SendToSouthEast/SIPI2/README/image-20230415004435432.png

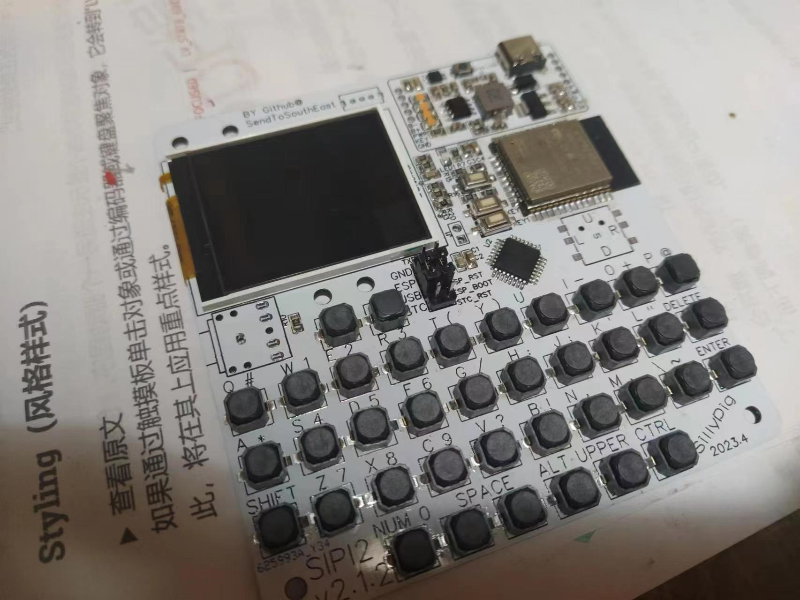
README/image-20230415004435432.png
