SendToSouthEast/SIPI2/README/image-20230421204047244.png

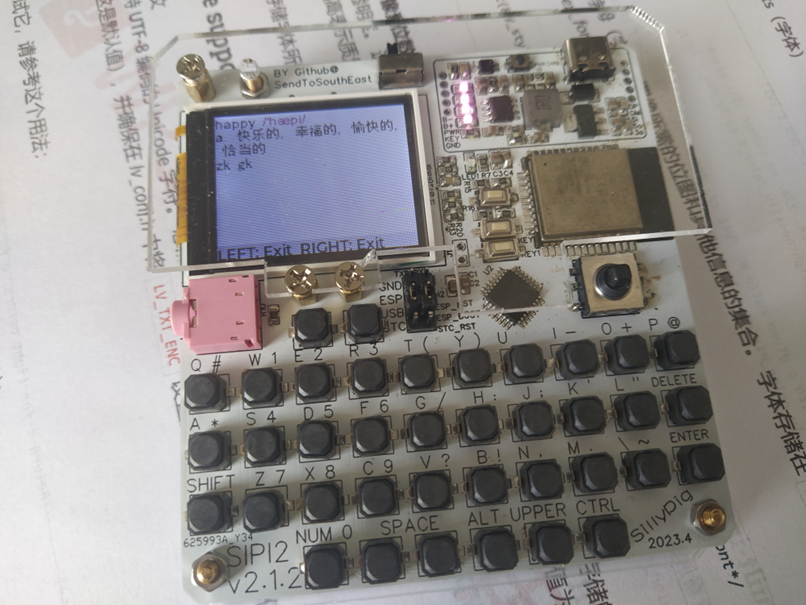
README/image-20230421204047244.png
