SendToSouthEast/SIPI2/SIPI2_ESP32/main/arial.c

/*******************************************************************************
 * Size: 12 px
 * Bpp: 1
 * Opts: 
 ******************************************************************************/

#ifdef LV_LVGL_H_INCLUDE_SIMPLE
#include "lvgl.h"
#else
#include "lvgl/lvgl.h"
#endif

#ifndef ARIAL
#define ARIAL 1
#endif

#if ARIAL

/*-----------------
 *    BITMAPS
 *----------------*/

/*Store the image of the glyphs*/
static LV_ATTRIBUTE_LARGE_CONST const uint8_t glyph_bitmap[] = {
    /* U+0020 " " */
    0x0,

    /* U+0027 "'" */
    0xe0,

    /* U+002C "," */
    0xc0,

    /* U+002D "-" */
    0xe0,

    /* U+002E "." */
    0x80,

    /* U+002F "/" */
    0x24, 0xa4, 0xa4,

    /* U+003A ":" */
    0x84,

    /* U+0041 "A" */
    0x18, 0x18, 0x2c, 0x24, 0x64, 0x7e, 0x42, 0x83,

    /* U+0042 "B" */
    0xfa, 0x18, 0x7e, 0x86, 0x18, 0x7e,

    /* U+0043 "C" */
    0x3c, 0x8e, 0x4, 0x8, 0x10, 0x51, 0x9e,

    /* U+0044 "D" */
    0xf9, 0xa, 0xc, 0x18, 0x30, 0x61, 0x7c,

    /* U+0045 "E" */
    0xfe, 0x8, 0x3f, 0x82, 0x8, 0x3f,

    /* U+0046 "F" */
    0xfe, 0x8, 0x3e, 0x82, 0x8, 0x20,

    /* U+0047 "G" */
    0x3c, 0x43, 0x81, 0x80, 0x8f, 0x81, 0x41, 0x3e,

    /* U+0048 "H" */
    0x83, 0x6, 0xf, 0xf8, 0x30, 0x60, 0xc1,

    /* U+0049 "I" */
    0xff,

    /* U+004A "J" */
    0x8, 0x42, 0x10, 0x86, 0x2e,

    /* U+004B "K" */
    0x85, 0x12, 0x47, 0xd, 0x11, 0x23, 0x43,

    /* U+004C "L" */
    0x84, 0x21, 0x8, 0x42, 0x1f,

    /* U+004D "M" */
    0xc3, 0xc3, 0xc3, 0xa5, 0xa5, 0x99, 0x99, 0x99,

    /* U+004E "N" */
    0x83, 0x86, 0x8d, 0x99, 0xb1, 0x61, 0xc1,

    /* U+004F "O" */
    0x3c, 0x42, 0x81, 0x81, 0x81, 0x81, 0x42, 0x3c,

    /* U+0050 "P" */
    0xfa, 0x18, 0x61, 0xfa, 0x8, 0x20,

    /* U+0051 "Q" */
    0x3c, 0x42, 0x81, 0x81, 0x81, 0x81, 0x4e, 0x3f,

    /* U+0052 "R" */
    0xfc, 0x82, 0x82, 0xfc, 0x88, 0x84, 0x86, 0x82,

    /* U+0053 "S" */
    0x7a, 0x38, 0x18, 0x1e, 0x18, 0x5e,

    /* U+0054 "T" */
    0xfe, 0x20, 0x40, 0x81, 0x2, 0x4, 0x8,

    /* U+0055 "U" */
    0x83, 0x6, 0xc, 0x18, 0x30, 0x71, 0xbe,

    /* U+0056 "V" */
    0x81, 0x42, 0x42, 0x64, 0x24, 0x24, 0x18, 0x18,

    /* U+0057 "W" */
    0x86, 0x28, 0xc5, 0x29, 0x25, 0x24, 0x94, 0x62,
    0x8c, 0x61, 0x84,

    /* U+0058 "X" */
    0x42, 0x24, 0x3c, 0x18, 0x18, 0x24, 0x66, 0xc3,

    /* U+0059 "Y" */
    0x82, 0x89, 0xb1, 0x41, 0x2, 0x4, 0x8,

    /* U+005A "Z" */
    0xfe, 0x8, 0x20, 0x82, 0xc, 0x30, 0x7f,

    /* U+0061 "a" */
    0x74, 0x47, 0xd8, 0xfc,

    /* U+0062 "b" */
    0x84, 0x3d, 0x18, 0xc6, 0x3e,

    /* U+0063 "c" */
    0x76, 0x61, 0x8, 0xb8,

    /* U+0064 "d" */
    0x8, 0x5f, 0x18, 0xc6, 0x2f,

    /* U+0065 "e" */
    0x72, 0x2f, 0xa0, 0xc9, 0xe0,

    /* U+0066 "f" */
    0x74, 0xe4, 0x44, 0x44,

    /* U+0067 "g" */
    0x7c, 0x63, 0x18, 0xbe, 0x2e,

    /* U+0068 "h" */
    0x84, 0x3d, 0x18, 0xc6, 0x31,

    /* U+0069 "i" */
    0xbf,

    /* U+006A "j" */
    0x45, 0x55, 0x70,

    /* U+006B "k" */
    0x84, 0x25, 0x4e, 0x52, 0x53,

    /* U+006C "l" */
    0xff,

    /* U+006D "m" */
    0xf7, 0x44, 0x62, 0x31, 0x18, 0x8c, 0x44,

    /* U+006E "n" */
    0xf4, 0x63, 0x18, 0xc4,

    /* U+006F "o" */
    0x7b, 0x38, 0x61, 0xcd, 0xe0,

    /* U+0070 "p" */
    0xf6, 0x63, 0x18, 0xfa, 0x10,

    /* U+0071 "q" */
    0x7c, 0xe3, 0x18, 0xbc, 0x21,

    /* U+0072 "r" */
    0xf2, 0x49, 0x0,

    /* U+0073 "s" */
    0x74, 0x78, 0x38, 0xb8,

    /* U+0074 "t" */
    0x4b, 0xa4, 0x93,

    /* U+0075 "u" */
    0x8c, 0x63, 0x18, 0xbc,

    /* U+0076 "v" */
    0x85, 0x24, 0x8c, 0x30, 0xc0,

    /* U+0077 "w" */
    0x89, 0x2c, 0x95, 0x4a, 0xc6, 0x61, 0x30,

    /* U+0078 "x" */
    0x49, 0xe3, 0xc, 0x4b, 0x30,

    /* U+0079 "y" */
    0xc5, 0x24, 0x8c, 0x30, 0xc2, 0x18,

    /* U+007A "z" */
    0xfc, 0x21, 0x8, 0x43, 0xf0,

    /* U+00E6 "æ" */
    0x77, 0xa2, 0x17, 0xfe, 0x20, 0x9c, 0xdd, 0xe0,

    /* U+014B "ŋ" */
    0xf4, 0x63, 0x18, 0xc4, 0x23,

    /* U+0251 "ɑ" */
    0x7c, 0x63, 0x18, 0xbc,

    /* U+0252 "ɒ" */
    0xf4, 0x63, 0x18, 0xf8,

    /* U+0254 "ɔ" */
    0x74, 0x42, 0x18, 0xb8,

    /* U+0259 "ə" */
    0x79, 0x30, 0x7f, 0x44, 0xe0,

    /* U+025A "ɚ" */
    0x78, 0x46, 0x1f, 0x90, 0xf8, 0xc3, 0xc0,

    /* U+025B "ɛ" */
    0xf9, 0x68, 0x97,

    /* U+025C "ɜ" */
    0xf9, 0x61, 0x9e,

    /* U+026A "ɪ" */
    0xe9, 0x25, 0xc0,

    /* U+0275 "ɵ" */
    0x7a, 0x1f, 0xe1, 0xcd, 0xe0,

    /* U+0283 "ʃ" */
    0x74, 0x44, 0x44, 0x44, 0x4c,

    /* U+028A "ʊ" */
    0xcd, 0x28, 0x61, 0xcd, 0xe0,

    /* U+028C "ʌ" */
    0x30, 0xc3, 0x12, 0x4a, 0x10,

    /* U+0292 "ʒ" */
    0x7c, 0x21, 0xe, 0x4, 0x14, 0xce,

    /* U+02C8 "ˈ" */
    0xc0,

    /* U+02CC "ˌ" */
    0xc0,

    /* U+02D0 "ː" */
    0x84,

    /* U+0303 "̃" */
    0xe0,

    /* U+0329 "̩" */
    0xc0,

    /* U+04D9 "ә" */
    0x79, 0x30, 0x7f, 0x44, 0xe0
};


/*---------------------
 *  GLYPH DESCRIPTION
 *--------------------*/

static const lv_font_fmt_txt_glyph_dsc_t glyph_dsc[] = {
    {.bitmap_index = 0, .adv_w = 0, .box_w = 0, .box_h = 0, .ofs_x = 0, .ofs_y = 0} /* id = 0 reserved */,
    {.bitmap_index = 0, .adv_w = 53, .box_w = 1, .box_h = 1, .ofs_x = 0, .ofs_y = 0},
    {.bitmap_index = 1, .adv_w = 37, .box_w = 1, .box_h = 3, .ofs_x = 1, .ofs_y = 5},
    {.bitmap_index = 2, .adv_w = 53, .box_w = 1, .box_h = 3, .ofs_x = 1, .ofs_y = -2},
    {.bitmap_index = 3, .adv_w = 64, .box_w = 3, .box_h = 1, .ofs_x = 1, .ofs_y = 2},
    {.bitmap_index = 4, .adv_w = 53, .box_w = 1, .box_h = 1, .ofs_x = 1, .ofs_y = 0},
    {.bitmap_index = 5, .adv_w = 53, .box_w = 3, .box_h = 8, .ofs_x = 0, .ofs_y = 0},
    {.bitmap_index = 8, .adv_w = 53, .box_w = 1, .box_h = 6, .ofs_x = 1, .ofs_y = 0},
    {.bitmap_index = 9, .adv_w = 128, .box_w = 8, .box_h = 8, .ofs_x = 0, .ofs_y = 0},
    {.bitmap_index = 17, .adv_w = 128, .box_w = 6, .box_h = 8, .ofs_x = 1, .ofs_y = 0},
    {.bitmap_index = 23, .adv_w = 139, .box_w = 7, .box_h = 8, .ofs_x = 1, .ofs_y = 0},
    {.bitmap_index = 30, .adv_w = 139, .box_w = 7, .box_h = 8, .ofs_x = 1, .ofs_y = 0},
    {.bitmap_index = 37, .adv_w = 128, .box_w = 6, .box_h = 8, .ofs_x = 1, .ofs_y = 0},
    {.bitmap_index = 43, .adv_w = 117, .box_w = 6, .box_h = 8, .ofs_x = 1, .ofs_y = 0},
    {.bitmap_index = 49, .adv_w = 149, .box_w = 8, .box_h = 8, .ofs_x = 1, .ofs_y = 0},
    {.bitmap_index = 57, .adv_w = 139, .box_w = 7, .box_h = 8, .ofs_x = 1, .ofs_y = 0},
    {.bitmap_index = 64, .adv_w = 53, .box_w = 1, .box_h = 8, .ofs_x = 1, .ofs_y = 0},
    {.bitmap_index = 65, .adv_w = 96, .box_w = 5, .box_h = 8, .ofs_x = 1, .ofs_y = 0},
    {.bitmap_index = 70, .adv_w = 128, .box_w = 7, .box_h = 8, .ofs_x = 1, .ofs_y = 0},
    {.bitmap_index = 77, .adv_w = 107, .box_w = 5, .box_h = 8, .ofs_x = 1, .ofs_y = 0},
    {.bitmap_index = 82, .adv_w = 160, .box_w = 8, .box_h = 8, .ofs_x = 1, .ofs_y = 0},
    {.bitmap_index = 90, .adv_w = 139, .box_w = 7, .box_h = 8, .ofs_x = 1, .ofs_y = 0},
    {.bitmap_index = 97, .adv_w = 149, .box_w = 8, .box_h = 8, .ofs_x = 1, .ofs_y = 0},
    {.bitmap_index = 105, .adv_w = 128, .box_w = 6, .box_h = 8, .ofs_x = 1, .ofs_y = 0},
    {.bitmap_index = 111, .adv_w = 149, .box_w = 8, .box_h = 8, .ofs_x = 1, .ofs_y = 0},
    {.bitmap_index = 119, .adv_w = 139, .box_w = 8, .box_h = 8, .ofs_x = 1, .ofs_y = 0},
    {.bitmap_index = 127, .adv_w = 128, .box_w = 6, .box_h = 8, .ofs_x = 1, .ofs_y = 0},
    {.bitmap_index = 133, .adv_w = 117, .box_w = 7, .box_h = 8, .ofs_x = 0, .ofs_y = 0},
    {.bitmap_index = 140, .adv_w = 139, .box_w = 7, .box_h = 8, .ofs_x = 1, .ofs_y = 0},
    {.bitmap_index = 147, .adv_w = 128, .box_w = 8, .box_h = 8, .ofs_x = 0, .ofs_y = 0},
    {.bitmap_index = 155, .adv_w = 181, .box_w = 11, .box_h = 8, .ofs_x = 0, .ofs_y = 0},
    {.bitmap_index = 166, .adv_w = 128, .box_w = 8, .box_h = 8, .ofs_x = 0, .ofs_y = 0},
    {.bitmap_index = 174, .adv_w = 128, .box_w = 7, .box_h = 8, .ofs_x = 0, .ofs_y = 0},
    {.bitmap_index = 181, .adv_w = 117, .box_w = 7, .box_h = 8, .ofs_x = 1, .ofs_y = 0},
    {.bitmap_index = 188, .adv_w = 107, .box_w = 5, .box_h = 6, .ofs_x = 1, .ofs_y = 0},
    {.bitmap_index = 192, .adv_w = 107, .box_w = 5, .box_h = 8, .ofs_x = 1, .ofs_y = 0},
    {.bitmap_index = 197, .adv_w = 96, .box_w = 5, .box_h = 6, .ofs_x = 1, .ofs_y = 0},
    {.bitmap_index = 201, .adv_w = 107, .box_w = 5, .box_h = 8, .ofs_x = 1, .ofs_y = 0},
    {.bitmap_index = 206, .adv_w = 107, .box_w = 6, .box_h = 6, .ofs_x = 1, .ofs_y = 0},
    {.bitmap_index = 211, .adv_w = 53, .box_w = 4, .box_h = 8, .ofs_x = 0, .ofs_y = 0},
    {.bitmap_index = 215, .adv_w = 107, .box_w = 5, .box_h = 8, .ofs_x = 1, .ofs_y = -2},
    {.bitmap_index = 220, .adv_w = 107, .box_w = 5, .box_h = 8, .ofs_x = 1, .ofs_y = 0},
    {.bitmap_index = 225, .adv_w = 43, .box_w = 1, .box_h = 8, .ofs_x = 1, .ofs_y = 0},
    {.bitmap_index = 226, .adv_w = 43, .box_w = 2, .box_h = 10, .ofs_x = 0, .ofs_y = -2},
    {.bitmap_index = 229, .adv_w = 96, .box_w = 5, .box_h = 8, .ofs_x = 1, .ofs_y = 0},
    {.bitmap_index = 234, .adv_w = 43, .box_w = 1, .box_h = 8, .ofs_x = 1, .ofs_y = 0},
    {.bitmap_index = 235, .adv_w = 160, .box_w = 9, .box_h = 6, .ofs_x = 1, .ofs_y = 0},
    {.bitmap_index = 242, .adv_w = 107, .box_w = 5, .box_h = 6, .ofs_x = 1, .ofs_y = 0},
    {.bitmap_index = 246, .adv_w = 107, .box_w = 6, .box_h = 6, .ofs_x = 1, .ofs_y = 0},
    {.bitmap_index = 251, .adv_w = 107, .box_w = 5, .box_h = 8, .ofs_x = 1, .ofs_y = -2},
    {.bitmap_index = 256, .adv_w = 107, .box_w = 5, .box_h = 8, .ofs_x = 1, .ofs_y = -2},
    {.bitmap_index = 261, .adv_w = 64, .box_w = 3, .box_h = 6, .ofs_x = 1, .ofs_y = 0},
    {.bitmap_index = 264, .adv_w = 96, .box_w = 5, .box_h = 6, .ofs_x = 1, .ofs_y = 0},
    {.bitmap_index = 268, .adv_w = 53, .box_w = 3, .box_h = 8, .ofs_x = 0, .ofs_y = 0},
    {.bitmap_index = 271, .adv_w = 107, .box_w = 5, .box_h = 6, .ofs_x = 1, .ofs_y = 0},
    {.bitmap_index = 275, .adv_w = 96, .box_w = 6, .box_h = 6, .ofs_x = 0, .ofs_y = 0},
    {.bitmap_index = 280, .adv_w = 139, .box_w = 9, .box_h = 6, .ofs_x = 0, .ofs_y = 0},
    {.bitmap_index = 287, .adv_w = 96, .box_w = 6, .box_h = 6, .ofs_x = 0, .ofs_y = 0},
    {.bitmap_index = 292, .adv_w = 96, .box_w = 6, .box_h = 8, .ofs_x = 0, .ofs_y = -2},
    {.bitmap_index = 298, .adv_w = 96, .box_w = 6, .box_h = 6, .ofs_x = 1, .ofs_y = 0},
    {.bitmap_index = 303, .adv_w = 171, .box_w = 10, .box_h = 6, .ofs_x = 1, .ofs_y = 0},
    {.bitmap_index = 311, .adv_w = 107, .box_w = 5, .box_h = 8, .ofs_x = 1, .ofs_y = -2},
    {.bitmap_index = 316, .adv_w = 107, .box_w = 5, .box_h = 6, .ofs_x = 1, .ofs_y = 0},
    {.bitmap_index = 320, .adv_w = 107, .box_w = 5, .box_h = 6, .ofs_x = 1, .ofs_y = 0},
    {.bitmap_index = 324, .adv_w = 96, .box_w = 5, .box_h = 6, .ofs_x = 0, .ofs_y = 0},
    {.bitmap_index = 328, .adv_w = 107, .box_w = 6, .box_h = 6, .ofs_x = 0, .ofs_y = 0},
    {.bitmap_index = 333, .adv_w = 142, .box_w = 9, .box_h = 6, .ofs_x = 1, .ofs_y = 0},
    {.bitmap_index = 340, .adv_w = 88, .box_w = 4, .box_h = 6, .ofs_x = 1, .ofs_y = 0},
    {.bitmap_index = 343, .adv_w = 88, .box_w = 4, .box_h = 6, .ofs_x = 1, .ofs_y = 0},
    {.bitmap_index = 346, .adv_w = 68, .box_w = 3, .box_h = 6, .ofs_x = 1, .ofs_y = 0},
    {.bitmap_index = 349, .adv_w = 107, .box_w = 6, .box_h = 6, .ofs_x = 1, .ofs_y = 0},
    {.bitmap_index = 354, .adv_w = 43, .box_w = 4, .box_h = 10, .ofs_x = 0, .ofs_y = -2},
    {.bitmap_index = 359, .adv_w = 109, .box_w = 6, .box_h = 6, .ofs_x = 1, .ofs_y = 0},
    {.bitmap_index = 364, .adv_w = 96, .box_w = 6, .box_h = 6, .ofs_x = 0, .ofs_y = 0},
    {.bitmap_index = 369, .adv_w = 105, .box_w = 6, .box_h = 8, .ofs_x = 0, .ofs_y = -2},
    {.bitmap_index = 375, .adv_w = 64, .box_w = 1, .box_h = 2, .ofs_x = 2, .ofs_y = 6},
    {.bitmap_index = 376, .adv_w = 64, .box_w = 1, .box_h = 2, .ofs_x = 2, .ofs_y = -2},
    {.bitmap_index = 377, .adv_w = 53, .box_w = 1, .box_h = 6, .ofs_x = 1, .ofs_y = 0},
    {.bitmap_index = 378, .adv_w = 0, .box_w = 4, .box_h = 1, .ofs_x = -5, .ofs_y = 8},
    {.bitmap_index = 379, .adv_w = 0, .box_w = 1, .box_h = 2, .ofs_x = 0, .ofs_y = -2},
    {.bitmap_index = 380, .adv_w = 107, .box_w = 6, .box_h = 6, .ofs_x = 0, .ofs_y = 0}
};

/*---------------------
 *  CHARACTER MAPPING
 *--------------------*/

static const uint16_t unicode_list_0[] = {
    0x0, 0x7, 0xc, 0xd, 0xe, 0xf, 0x1a
};

static const uint16_t unicode_list_3[] = {
    0x0, 0x65, 0x16b, 0x16c, 0x16e, 0x173, 0x174, 0x175,
    0x176, 0x184, 0x18f, 0x19d, 0x1a4, 0x1a6, 0x1ac, 0x1e2,
    0x1e6, 0x1ea, 0x21d, 0x243, 0x3f3
};

/*Collect the unicode lists and glyph_id offsets*/
static const lv_font_fmt_txt_cmap_t cmaps[] =
{
    {
        .range_start = 32, .range_length = 27, .glyph_id_start = 1,
        .unicode_list = unicode_list_0, .glyph_id_ofs_list = NULL, .list_length = 7, .type = LV_FONT_FMT_TXT_CMAP_SPARSE_TINY
    },
    {
        .range_start = 65, .range_length = 26, .glyph_id_start = 8,
        .unicode_list = NULL, .glyph_id_ofs_list = NULL, .list_length = 0, .type = LV_FONT_FMT_TXT_CMAP_FORMAT0_TINY
    },
    {
        .range_start = 97, .range_length = 26, .glyph_id_start = 34,
        .unicode_list = NULL, .glyph_id_ofs_list = NULL, .list_length = 0, .type = LV_FONT_FMT_TXT_CMAP_FORMAT0_TINY
    },
    {
        .range_start = 230, .range_length = 1012, .glyph_id_start = 60,
        .unicode_list = unicode_list_3, .glyph_id_ofs_list = NULL, .list_length = 21, .type = LV_FONT_FMT_TXT_CMAP_SPARSE_TINY
    }
};



/*--------------------
 *  ALL CUSTOM DATA
 *--------------------*/

#if LV_VERSION_CHECK(8, 0, 0)
/*Store all the custom data of the font*/
static  lv_font_fmt_txt_glyph_cache_t cache;
static const lv_font_fmt_txt_dsc_t font_dsc = {
#else
static lv_font_fmt_txt_dsc_t font_dsc = {
#endif
    .glyph_bitmap = glyph_bitmap,
    .glyph_dsc = glyph_dsc,
    .cmaps = cmaps,
    .kern_dsc = NULL,
    .kern_scale = 0,
    .cmap_num = 4,
    .bpp = 1,
    .kern_classes = 0,
    .bitmap_format = 0,
#if LV_VERSION_CHECK(8, 0, 0)
    .cache = &cache
#endif
};


/*-----------------
 *  PUBLIC FONT
 *----------------*/

/*Initialize a public general font descriptor*/
#if LV_VERSION_CHECK(8, 0, 0)
const lv_font_t arial = {
#else
lv_font_t arial = {
#endif
    .get_glyph_dsc = lv_font_get_glyph_dsc_fmt_txt,    /*Function pointer to get glyph's data*/
    .get_glyph_bitmap = lv_font_get_bitmap_fmt_txt,    /*Function pointer to get glyph's bitmap*/
    .line_height = 11,          /*The maximum line height required by the font*/
    .base_line = 2,             /*Baseline measured from the bottom of the line*/
#if !(LVGL_VERSION_MAJOR == 6 && LVGL_VERSION_MINOR == 0)
    .subpx = LV_FONT_SUBPX_NONE,
#endif
#if LV_VERSION_CHECK(7, 4, 0) || LVGL_VERSION_MAJOR >= 8
    .underline_position = -1,
    .underline_thickness = 1,
#endif
    .dsc = &font_dsc           /*The custom font data. Will be accessed by `get_glyph_bitmap/dsc` */
};



#endif /*#if ARIAL*/
